ene9ba/IoT_LED-Matrix-64x64_p/Doc/photo_2024-04-16_13-58-55.jpg

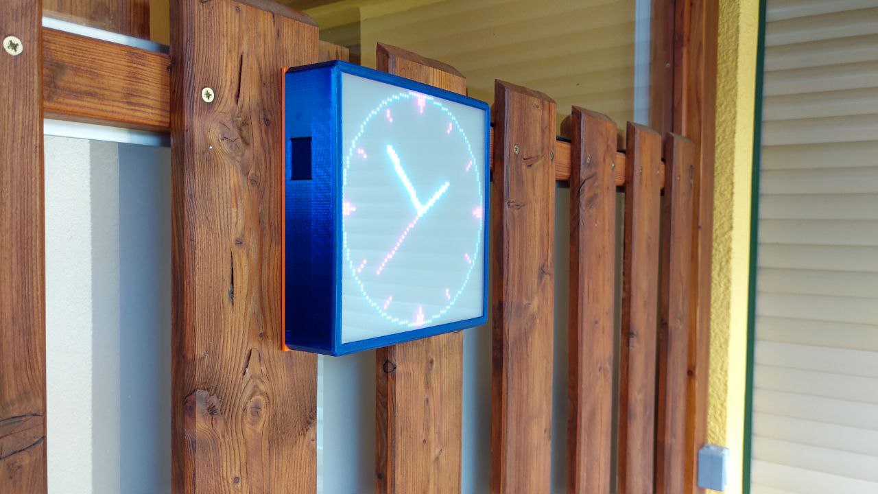
Doc/photo_2024-04-16_13-58-55.jpg
