ene9ba/IoT_LED-Matrix-64x64_p/Software/include/drawpicture.h

#include <Arduino.h>
// This is a horribly inefficient way of drawing this, but meh.. :)
// Converted using the following site: http://www.rinkydinkelectronics.com/t_imageconverter565.php
uint16_t static hottub[] = {
0x936B, 0x93AB, 0xAC4E, 0xA40E, 0xA42E, 0xA42F, 0x9BEE, 0x9BAB, 0xA40B, 0x9B89, 0x9348, 0x9B47, 0x9346, 0xDDAB, 0x9347, 0x8287,   // 0x0010 (16) pixels
0x8287, 0x936C, 0x8AC7, 0xCD8D, 0xDE2C, 0x9BA7, 0xDDCF, 0xDE31, 0xB368, 0xB3CA, 0xBBC9, 0xBC4B, 0xC4EF, 0xA347, 0xA3CB, 0x9B49,   // 0x0020 (32) pixels
0xC4CA, 0xABCB, 0x9B26, 0xBBE9, 0xAB89, 0xB3A9, 0xB386, 0xABA9, 0x9B47, 0xABA9, 0xB3E9, 0xAC0C, 0xABEC, 0xBC6D, 0xCC87, 0xD507,   // 0x0030 (48) pixels
0x9328, 0x9B28, 0x9329, 0xA3ED, 0x7AE9, 0x832A, 0x9BCC, 0xAC70, 0xC56F, 0x732E, 0xADFA, 0xCEDD, 0xAC4C, 0xA40C, 0xA3C9, 0xA306,   // 0x0040 (64) pixels
0x8307, 0x82A6, 0xB46E, 0x932A, 0xA40D, 0x9BAB, 0x8B2A, 0x9B8A, 0x938A, 0xABC7, 0x9BA8, 0x9327, 0x9BA8, 0xCD29, 0xB44A, 0x8AC7,   // 0x0050 (80) pixels
0x92C7, 0x9B29, 0x9B08, 0xC50A, 0xE68C, 0xA3A6, 0xCD0A, 0xD632, 0xB3C9, 0xAB68, 0xCC4A, 0xBCAF, 0xBC2B, 0xB3A9, 0xC48C, 0xABCB,   // 0x0060 (96) pixels
0xC489, 0xABEB, 0xAB89, 0xAB68, 0xB3EA, 0xAB88, 0xAB68, 0xB3EA, 0xB3A9, 0xB40B, 0xA3AA, 0x9B8B, 0xAC4F, 0xCD73, 0xCC85, 0xD4E6,   // 0x0070 (112) pixels
0x9BEC, 0xA40E, 0xBD32, 0xACB1, 0xB4F2, 0x93CD, 0xACB1, 0xBD33, 0xC56F, 0x62CD, 0xA5B9, 0xC67B, 0xA3CA, 0xA3AA, 0xC4EF, 0x92A5,   // 0x0080 (128) pixels
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
};






void drawImage(int x, int y)
{
  int imageHeight = 64;
  int imageWidth = 64;
  int counter = 0;
  for (int yy = 0; yy < imageHeight; yy++)
  {
    for (int xx = 0; xx < imageWidth; xx++)
    {
      matrix.drawPixel(xx + x , yy + y, hottub[counter]);
      counter++;
    }
  }
}
